TankedThomas/ZX80/ZX80_Board.kicad_sch

## KiCad design ZX80_Board.kicad_sch (2023-08-20, an earlier design)

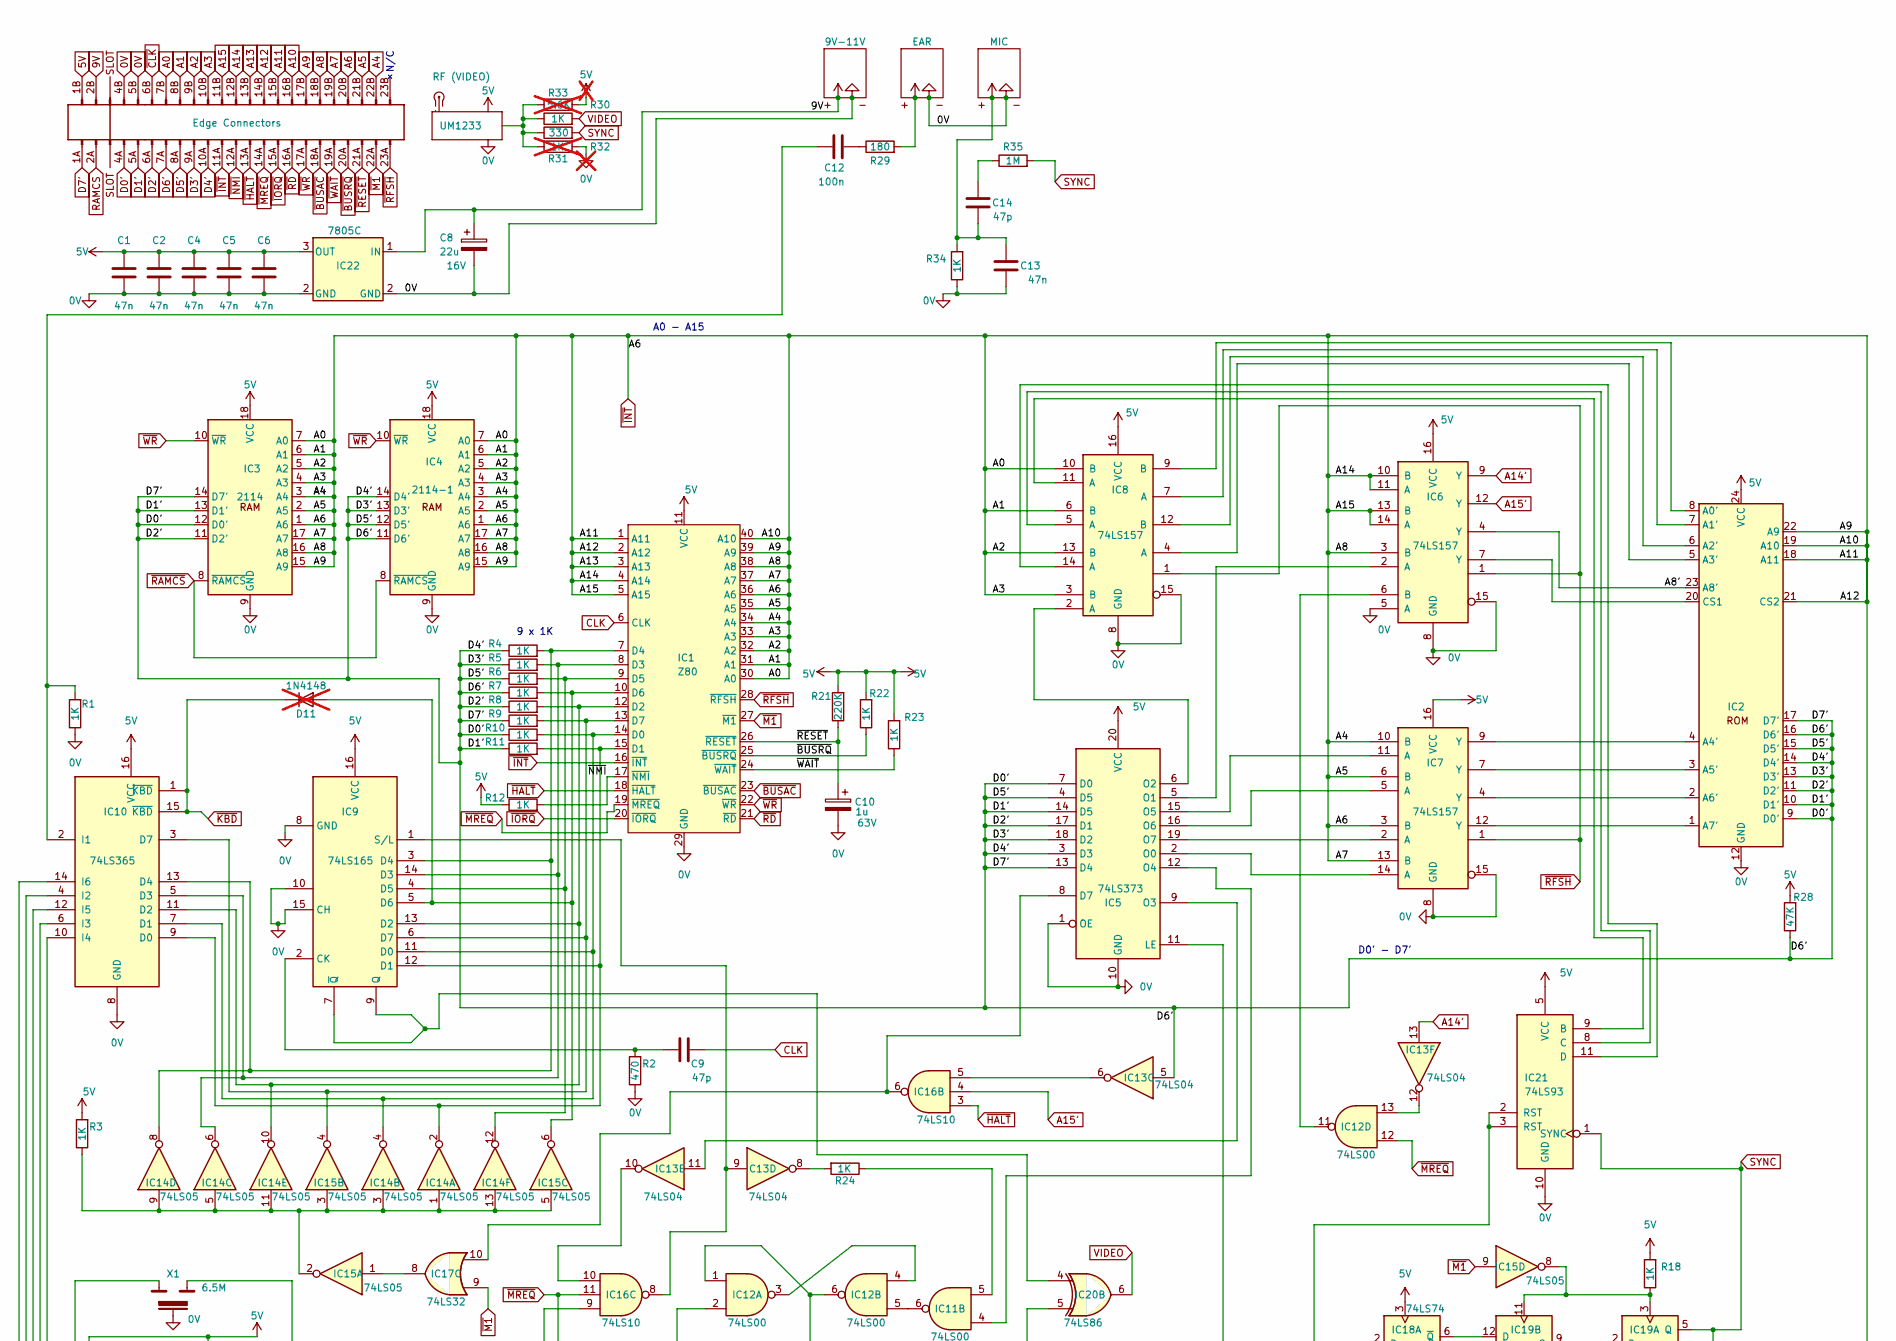
[picture p8: schematic ZX80_Board.kicad_sch, part in row 1, column 1]

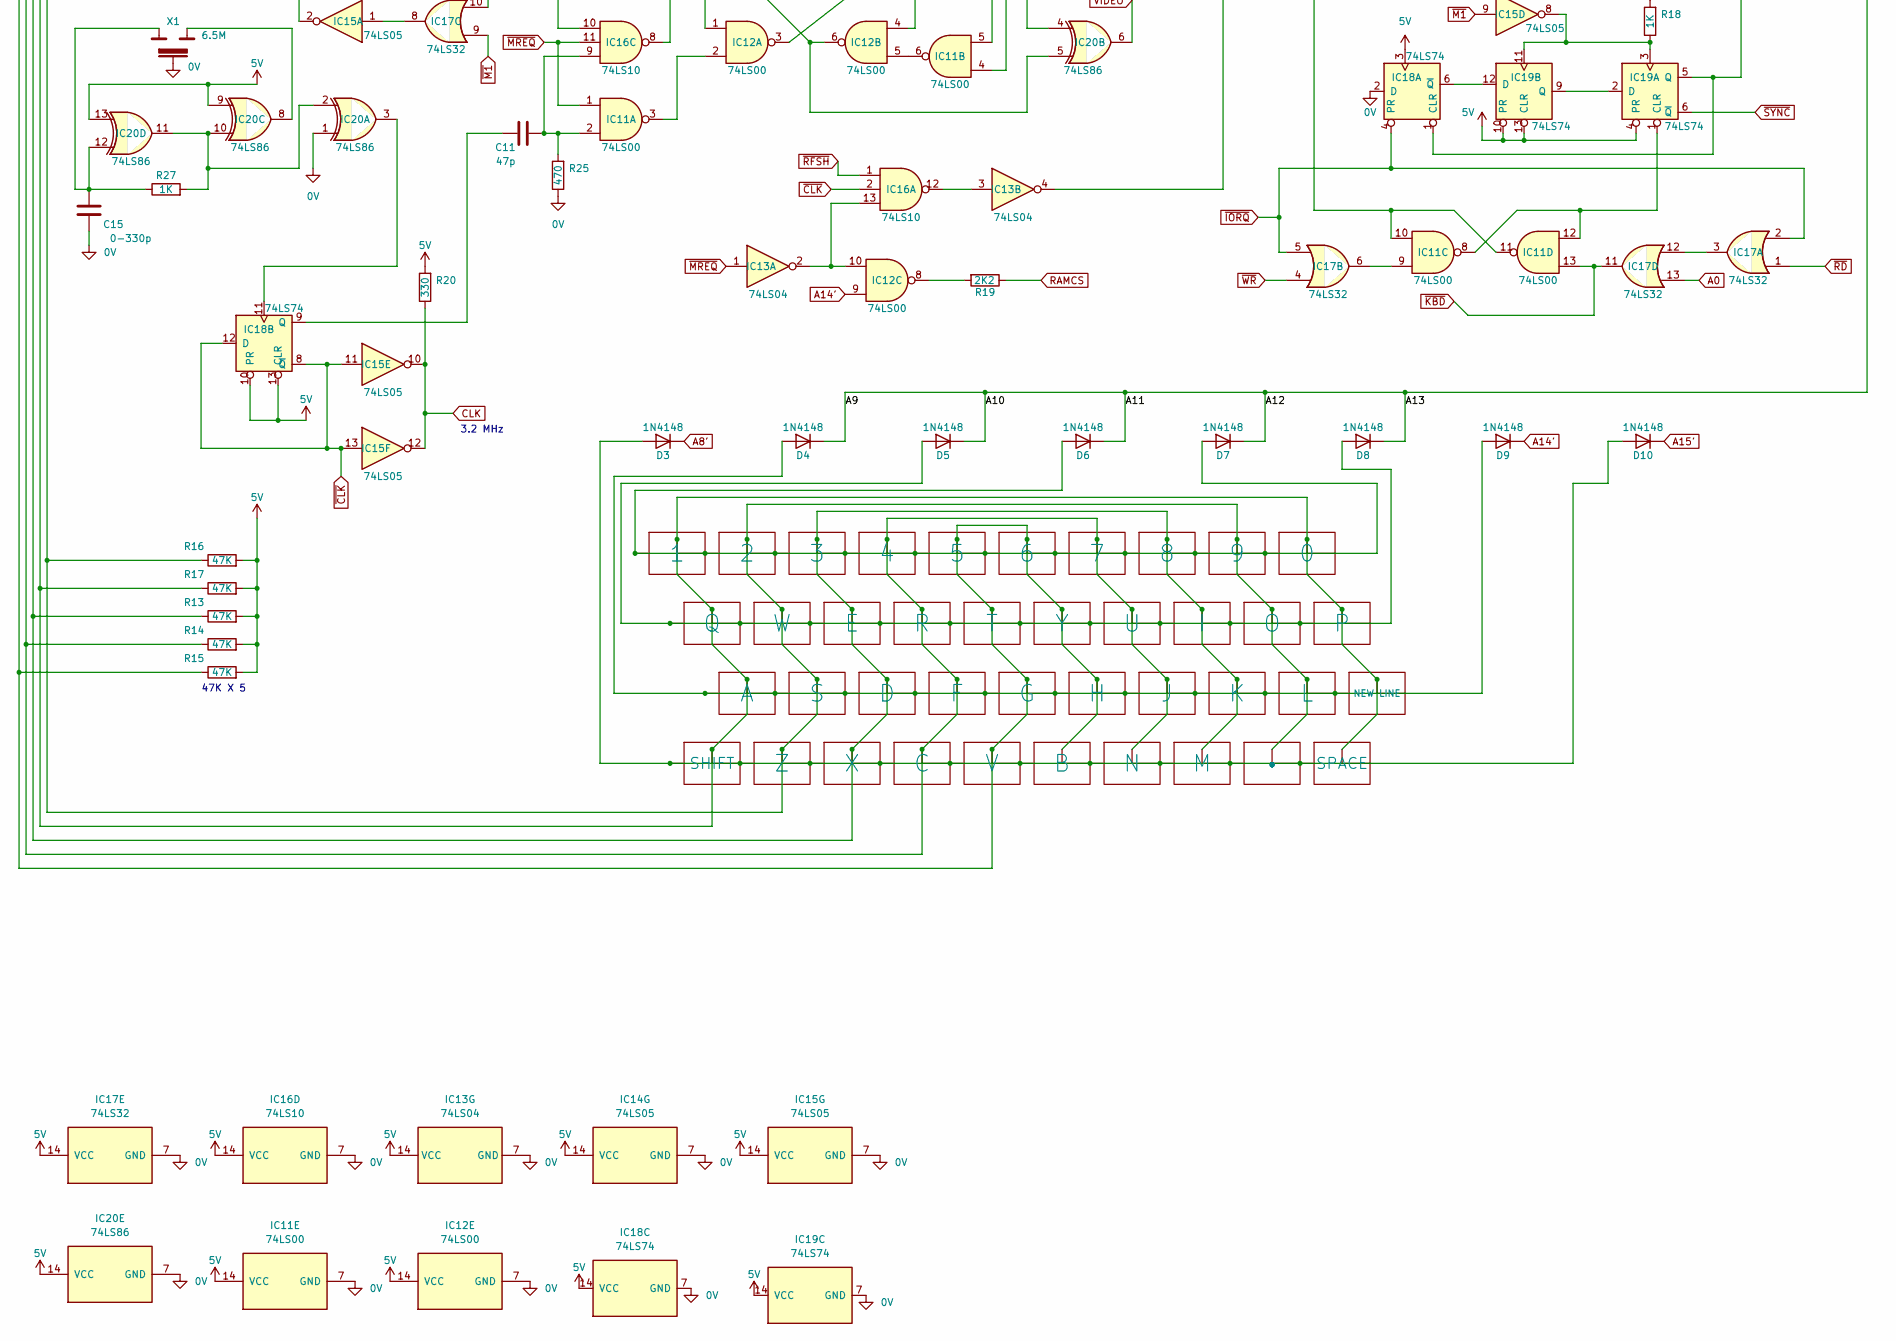
[picture p9: schematic ZX80_Board.kicad_sch, part in row 2, column 1]

Parts:
C1, C2, C4, C5, C6, C13: 47n; C_Disc_D5.0mm_W2.5mm_P2.50mm
C8: 22u; ZX80_C8_CP_Radial_D6.3mm_P3.50mm; Voltage 16V
C9, C11, C14: 47p; C_Disc_D5.0mm_W2.5mm_P2.50mm
C10: 1u; ZX80_C10_CP_Radial_D6.3mm_P3.50mm; Voltage 63V
C12: 100n; C_Disc_D5.0mm_W2.5mm_P2.50mm
C15: 0-330p; C_Disc_D5.0mm_W2.5mm_P2.50mm
D3, D4, D5, D6, D7, D8, D9, D10: 1N4148; D_DO-41_SOD81_P7.62mm_Horizontal
D11: 1N4148; D_DO-41_SOD81_P7.62mm_Horizontal; not fitted
EdgeConnector1: Edge Connectors; ZX80-EdgeConn_46P
IC1: Z80; DIP-40_W15.24mm
IC2: 8332; DIP-24_W15.24mm
IC3: 2114; DIP-18_W7.62mm
IC4: 2114-1; DIP-18_W7.62mm
IC5: 74LS373; DIP-20_W7.62mm
IC6, IC7, IC8: 74LS157; DIP-16_W7.62mm
IC9: 74LS165; DIP-16_W7.62mm
IC10: 74LS365; DIP-16_W7.62mm
IC11, IC12: 74LS00; DIP-14_W7.62mm
IC13: 74LS04; DIP-14_W7.62mm
IC14, IC15: 74LS05; DIP-14_W7.62mm
IC16: 74LS10; DIP-14_W7.62mm
IC17: 74LS32; DIP-14_W7.62mm
IC18, IC19: 74LS74; DIP-14_W7.62mm
IC20: 74LS86; DIP-14_W7.62mm
IC21: 74LS93; DIP-14_W7.62mm
IC22: 7805C; TO-220-3_Horizontal_TabDown
J1: 9V-11V; PhonoConn_3Pin
J2: EAR; PhonoConn_3Pin
J3: MIC; PhonoConn_3Pin
R1, R3, R4, R5, R6, R7, R8, R9, R10, R11, R12, R18, R22, R23, R24, R27, R30, R34: 1K; R_Axial_DIN0207_L6.3mm_D2.5mm_P7.62mm_Horizontal
R2, R25: 470; R_Axial_DIN0207_L6.3mm_D2.5mm_P7.62mm_Horizontal
R13, R14, R15, R16, R17, R28: 47K; R_Axial_DIN0207_L6.3mm_D2.5mm_P7.62mm_Horizontal
R19: 2K2; R_Axial_DIN0207_L6.3mm_D2.5mm_P7.62mm_Horizontal
R20, R32: 330; R_Axial_DIN0207_L6.3mm_D2.5mm_P7.62mm_Horizontal
R21: 220K; R_Axial_DIN0207_L6.3mm_D2.5mm_P7.62mm_Horizontal
R29: 180; R_Axial_DIN0207_L6.3mm_D2.5mm_P7.62mm_Horizontal
R31: 1K; R_Axial_DIN0207_L6.3mm_D2.5mm_P7.62mm_Horizontal; not fitted
R33: 5.6K; R_Axial_DIN0207_L6.3mm_D2.5mm_P7.62mm_Horizontal; not fitted
R35: 1M; R_Axial_DIN0207_L6.3mm_D2.5mm_P7.62mm_Horizontal
RF_MODULATOR1: UM1233; UM1233_RF_Modulator
SW1: 1; ZX80_Keypad
SW2: 2; ZX80_Keypad
SW3: 3; ZX80_Keypad
SW4: 4; ZX80_Keypad
SW5: 5; ZX80_Keypad
SW6: 6; ZX80_Keypad
SW7: 7; ZX80_Keypad
SW8: 8; ZX80_Keypad
SW9: 9; ZX80_Keypad
SW10: 0; ZX80_Keypad
SW11: Q; ZX80_Keypad
SW12: W; ZX80_Keypad
SW13: E; ZX80_Keypad
SW14: R; ZX80_Keypad
SW15: T; ZX80_Keypad
SW16: Y; ZX80_Keypad
SW17: U; ZX80_Keypad
SW18: I; ZX80_Keypad
SW19: O; ZX80_Keypad
SW20: P; ZX80_Keypad
SW21: A; ZX80_Keypad
SW22: S; ZX80_Keypad
SW23: D; ZX80_Keypad
SW24: F; ZX80_Keypad
SW25: G; ZX80_Keypad
SW26: H; ZX80_Keypad
SW27: J; ZX80_Keypad
SW28: K; ZX80_Keypad
SW29: L; ZX80_Keypad
SW30: NEW LINE; ZX80_Keypad
SW31: SHIFT; ZX80_Keypad
SW32: Z; ZX80_Keypad
SW33: X; ZX80_Keypad
SW34: C; ZX80_Keypad
SW35: V; ZX80_Keypad
SW36: B; ZX80_Keypad
SW37: N; ZX80_Keypad
SW38: M; ZX80_Keypad
SW39: •; ZX80_Keypad
SW40: SPACE; ZX80_Keypad
X1: 6.5M; Resonator-3Pin_W7.0mm_H2.5mm

Connections:
0V: C1.2, C2.2, C4.2, C5.2, C6.2, C8.2, C10.2, C13.1, C15.1, EdgeConnector1.4B (GND), EdgeConnector1.5B (GND), IC1.29 (GND), IC2.12 (GND), IC3.9 (GND), IC4.9 (GND), IC5.1 (OE), IC5.10 (GND), IC6.5 (A), IC6.8 (GND), IC6.15, IC7.8 (GND), IC7.15, IC8.8 (GND), IC8.15, IC9.8 (GND), IC9.10, IC9.15 (CH), IC10.8 (GND), IC11.7 (GND), IC12.7 (GND), IC13.7 (GND), IC14.7 (GND), IC15.7 (GND), IC16.7 (GND), IC17.7 (GND), IC18.2 (D), IC18.7 (GND), IC19.7 (GND), IC20.1, IC20.7 (GND), IC21.10 (GND), IC22.2 (GND), J1.R (RING), J1.S (SLEEVE), J2.R (RING), J2.S (SLEEVE), J3.R (RING), J3.S (SLEEVE), R1.1, R2.1, R25.1, R31.1, R34.1, RF_MODULATOR1.2 (0V), X1.2
5V: C1.1, C2.1, C4.1, C5.1, C6.1, C13.2, C14.1, EdgeConnector1.1B (5V), IC1.11 (VCC), IC2.24 (VCC), IC3.18 (VCC), IC4.18 (VCC), IC5.20 (VCC), IC6.16 (VCC), IC7.16 (VCC), IC8.16 (VCC), IC9.16 (VCC), IC10.16 (VCC), IC11.14 (VCC), IC12.14 (VCC), IC13.14 (VCC), IC14.14 (VCC), IC15.14 (VCC), IC16.14 (VCC), IC17.14 (VCC), IC18.3, IC18.10 (PR), IC18.13 (CLR), IC18.14 (VCC), IC19.4 (PR), IC19.10 (PR), IC19.13 (CLR), IC19.14 (VCC), IC20.9, IC20.13, IC20.14 (VCC), IC21.5 (VCC), IC22.3 (OUT), J2.T (TIP), J3.T (TIP), R3.2, R12.1, R13.2, R14.2, R15.2, R16.2, R17.2, R18.2, R20.2, R21.2, R22.2, R23.2, R28.2, R29.2, R33.2, R34.2, RF_MODULATOR1.1 (5V)
9V: C8.1, EdgeConnector1.2B (9V), IC22.1 (IN), J1.T (TIP)
A0: EdgeConnector1.7B (A0), IC17.13
A1: EdgeConnector1.8B (A1)
A2: EdgeConnector1.9B (A2)
A3: EdgeConnector1.10B (A3)
A4: EdgeConnector1.22B (A4)
A5: EdgeConnector1.21B (A5)
A6: EdgeConnector1.20B (A6)
A7: EdgeConnector1.19B (A7)
A8: EdgeConnector1.18B (A8)
A8': D3.2 (K), IC2.23 (A8'), IC6.4 (Y)
A9: EdgeConnector1.17B (A9)
A10: EdgeConnector1.16B (A10)
A11: EdgeConnector1.15B (A11)
A12: EdgeConnector1.14B (A12)
A13: EdgeConnector1.13B (A13)
A14: EdgeConnector1.12B (A14)
A14': D9.2 (K), IC6.9 (Y), IC12.9, IC13.13
A15: EdgeConnector1.11B (A15)
A15': D10.2 (K), IC6.12 (Y), IC16.4
CLK: C9.2, IC1.6 (CLK), IC15.10, IC15.12, R20.1
D0': EdgeConnector1.4A (D0'), IC2.9 (D0'), IC2.10 (D1'), IC2.11 (D2'), IC2.13 (D3'), IC2.14 (D4'), IC2.15 (D5'), IC2.16 (D6'), IC2.17 (D7'), IC3.11 (D2'), IC3.12 (D0'), IC3.13 (D1'), IC3.14 (D7'), IC4.11 (D6'), IC4.12 (D5'), IC4.13 (D3'), IC4.14 (D4'), IC5.3 (D3), IC5.4 (D5), IC5.7 (D0), IC5.13 (D4), IC5.14 (D5), IC5.17 (D1), IC5.18 (D2), IC13.5, R4.1, R5.1, R6.1, R7.1, R8.1, R9.1, R10.1, R11.1, R28.1
D1': EdgeConnector1.5A (D1')
D2': EdgeConnector1.6A (D2')
D3': EdgeConnector1.9A (D3')
D4': EdgeConnector1.10A (D4')
D5': EdgeConnector1.8A (D5')
D6': EdgeConnector1.7A (D6')
D7': EdgeConnector1.1A (D7')
unnamed: C9.1, IC9.2 (CK), R2.2
unnamed: C11.1, IC18.9 (Q)
unnamed: C11.2, IC11.2, IC16.9, R25.2
unnamed: C12.1, IC10.2 (I1), R1.2
unnamed: C12.2, R29.1
unnamed: C14.2, R35.1
unnamed: C15.2, IC20.12, R27.1, X1.1
unnamed: D4.1 (A), D9.1 (A), SW21.1, SW22.1, SW23.1, SW24.1, SW25.1, SW26.1, SW27.1, SW28.1, SW29.1, SW30.1
unnamed: D5.1 (A), D8.1 (A), SW11.1, SW12.1, SW13.1, SW14.1, SW15.1, SW16.1, SW17.1, SW18.1, SW19.1, SW20.1
unnamed: D6.1 (A), D7.1 (A), SW1.1, SW2.1, SW3.1, SW4.1, SW5.1, SW6.1, SW7.1, SW8.1, SW9.1, SW10.1
unnamed: D3.1 (A), D10.1 (A), SW31.1, SW32.1, SW33.1, SW34.1, SW35.1, SW36.1, SW37.1, SW38.1, SW39.1, SW40.1
unnamed: D11.1 (A), IC1.10 (D6), IC9.5 (D6), IC15.6, R7.2
unnamed: IC1.7 (D4), IC9.3 (D4), IC10.13 (D4), IC14.8, R4.2
unnamed: IC1.8 (D3), IC9.14 (D3), IC10.5 (D3), IC14.6, R5.2
unnamed: IC1.9 (D5), IC9.4 (D5), IC14.12, R6.2
unnamed: IC1.12 (D2), IC9.13 (D2), IC10.11 (D2), IC14.10, R8.2
unnamed: IC1.13 (D7), IC9.6 (D7), IC10.3 (D7), IC15.4, R9.2
unnamed: IC1.14 (D0), IC9.11 (D0), IC10.7 (D1), IC14.4, R10.2
unnamed: IC1.15 (D1), IC9.12 (D1), IC10.9 (D0), IC14.2, R11.2
unnamed: IC2.1 (A7'), IC7.12 (Y)
unnamed: IC2.2 (A6'), IC7.4 (Y)
unnamed: IC2.3 (A5'), IC7.7 (Y)
unnamed: IC2.4 (A4'), IC7.9 (Y)
unnamed: IC2.5 (A3'), IC8.4 (A)
unnamed: IC2.6 (A2'), IC8.12 (B)
unnamed: IC2.7 (A1'), IC8.7 (A)
unnamed: IC2.8 (A0'), IC8.9 (B)
unnamed: IC2.20 (CS1), IC6.7 (Y)
unnamed: IC5.2 (O0), IC7.14 (A)
unnamed: IC5.5 (O1), IC6.2 (A)
unnamed: IC5.6 (O2), IC8.2 (A)
unnamed: IC5.15 (O5), IC7.11 (A)
unnamed: IC5.16 (O6), IC7.5 (A)
unnamed: IC5.19 (O7), IC7.2 (A)
unnamed: IC10.4 (I2), R14.1, SW4.2, SW7.2, SW14.2, SW17.2, SW24.2, SW27.2, SW34.2, SW37.2
unnamed: IC10.6 (I3), R17.1, SW1.2, SW10.2, SW11.2, SW20.2, SW21.2, SW30.2, SW31.2, SW40.2
unnamed: IC10.10 (I4), R16.1, SW2.2, SW9.2, SW12.2, SW19.2, SW22.2, SW29.2, SW32.2, SW39.2
unnamed: IC10.12 (I5), R13.1, SW3.2, SW8.2, SW13.2, SW18.2, SW23.2, SW28.2, SW33.2, SW38.2
unnamed: IC10.14 (I6), R15.1, SW5.2, SW6.2, SW15.2, SW16.2, SW25.2, SW26.2, SW35.2, SW36.2
unnamed: IC11.3, IC12.2
unnamed: IC5.12 (O4), IC11.4
unnamed: IC11.5, R24.1
unnamed: IC11.6, IC12.5
unnamed: IC11.9, IC17.6
unnamed: IC11.10, IC11.11, IC21.2 (RST), IC21.3 (RST)
unnamed: IC11.8, IC11.12, IC19.1 (CLR)
unnamed: IC12.1, IC12.6, IC20.5
unnamed: IC12.3, IC12.4
unnamed: IC12.8, R19.2
unnamed: IC12.10, IC13.2, IC16.13
unnamed: IC6.6 (B), IC12.11
unnamed: IC12.13, IC13.12
unnamed: IC13.3, IC16.12
unnamed: IC5.11 (LE), IC13.4
unnamed: IC13.6, IC16.5
unnamed: IC13.8, R24.2
unnamed: IC9.1 (S/L), IC13.9, IC16.8
unnamed: IC13.10, IC16.10
unnamed: IC5.9 (O3), IC13.11
unnamed: IC14.1, IC14.3, IC14.5, IC14.9, IC14.11, IC14.13, IC15.2, IC15.3, IC15.5, R3.1
unnamed: IC15.1, IC17.8
unnamed: IC15.8, IC19.3, IC19.11, R18.1
unnamed: IC5.8 (D7), IC16.6, IC17.10
unnamed: IC17.3, IC17.12
unnamed: IC18.6 (~Q), IC19.12 (D)
unnamed: IC18.11, IC20.3
unnamed: IC19.2 (D), IC19.9 (Q)
unnamed: IC9.7 (~Q), IC9.9 (Q), IC20.4
unnamed: IC20.8, X1.3
unnamed: IC20.2, IC20.10, IC20.11, R27.2
unnamed: IC8.5 (A), IC21.8 (C)
unnamed: IC8.11 (A), IC21.9 (B)
unnamed: IC8.14 (A), IC21.11 (D)
unnamed: R30.1, R31.2, R32.1, R33.1, RF_MODULATOR1.3 (VIDEO)
RAMCS: EdgeConnector1.2A (~RAMCS), R19.1
SYNC: IC18.1 (CLR), IC19.5 (Q), IC21.1 (SYNC), R32.2, R35.2
VIDEO: IC20.6, R30.2
~BUSAC: EdgeConnector1.18A (~BUSAC), IC1.23 (~BUSAC)
~BUSRQ: EdgeConnector1.20A (~BUSRQ), IC1.25 (~BUSRQ), R22.1
~CLK: EdgeConnector1.6B (~CLK), IC15.11, IC15.13, IC16.2, IC18.8 (~Q), IC18.12 (D)
~HALT: EdgeConnector1.13A (~MALT), IC1.18 (~HALT), IC16.3
~INT: D4.2 (K), D5.2 (K), D6.2 (K), D7.2 (K), D8.2 (K), EdgeConnector1.11A (~INT), IC1.1 (A11), IC1.2 (A12), IC1.3 (A13), IC1.4 (A14), IC1.5 (A15), IC1.16 (~INT), IC1.30 (A0), IC1.31 (A1), IC1.32 (A2), IC1.33 (A3), IC1.34 (A4), IC1.35 (A5), IC1.36 (A6), IC1.37 (A7), IC1.38 (A8), IC1.39 (A9), IC1.40 (A10), IC2.18 (A11), IC2.19 (A10), IC2.21 (CS2), IC2.22 (A9), IC3.1 (A6), IC3.2 (A5), IC3.3 (A4), IC3.4 (A3), IC3.5 (A2), IC3.6 (A1), IC3.7 (A0), IC3.15 (A9), IC3.16 (A8), IC3.17 (A7), IC4.1 (A6), IC4.2 (A5), IC4.3 (A4), IC4.4 (A3), IC4.5 (A2), IC4.6 (A1), IC4.7 (A0), IC4.15 (A9), IC4.16 (A8), IC4.17 (A7), IC6.3 (B), IC6.10 (B), IC6.11 (A), IC6.13 (B), IC6.14 (A), IC7.3 (B), IC7.6 (B), IC7.10 (B), IC7.13 (B), IC8.3 (B), IC8.6 (B), IC8.10 (B), IC8.13 (B)
~IORQ: EdgeConnector1.15A (~IORQ), IC1.20 (~IORQ), IC17.2, IC17.5, IC18.4 (PR)
~KBD: D11.2 (K), IC10.1 (~KBD), IC10.15 (~KBD), IC11.13, IC17.11
~M1: EdgeConnector1.22A (~M1), IC1.27 (~M1), IC15.9, IC17.9
~MREQ: EdgeConnector1.14A (~MREQ), IC1.19 (~MREQ), IC11.1, IC12.12, IC13.1, IC16.11
~NMI: EdgeConnector1.12A (~NMI), IC1.17 (~NMI), R12.2
~RAMCS: IC3.8 (~RAMCS), IC4.8 (~RAMCS)
~RD: EdgeConnector1.16A (~RD), IC1.21 (~RD), IC17.1
~RESET: C10.1, EdgeConnector1.21A (~RESET), IC1.26 (~RESET), R21.1
~RFSH: EdgeConnector1.23A (~REFSH), IC1.28 (~RFSH), IC6.1, IC7.1, IC8.1, IC16.1
~SYNC: IC19.6 (~Q)
~WAIT: EdgeConnector1.19A (~WAIT), IC1.24 (~WAIT), R23.1
~WR: EdgeConnector1.17A (~WR), IC1.22 (~WR), IC3.10 (~WR), IC4.10 (~WR), IC17.4

Notes on the sheet:
9 x 1K
A0 - A15
D0' - D7'
N/C
47K X 5
3.2 MHz
~{}
